LegacyNsfw/AvcsController/Docs/2013 STI Signals.png

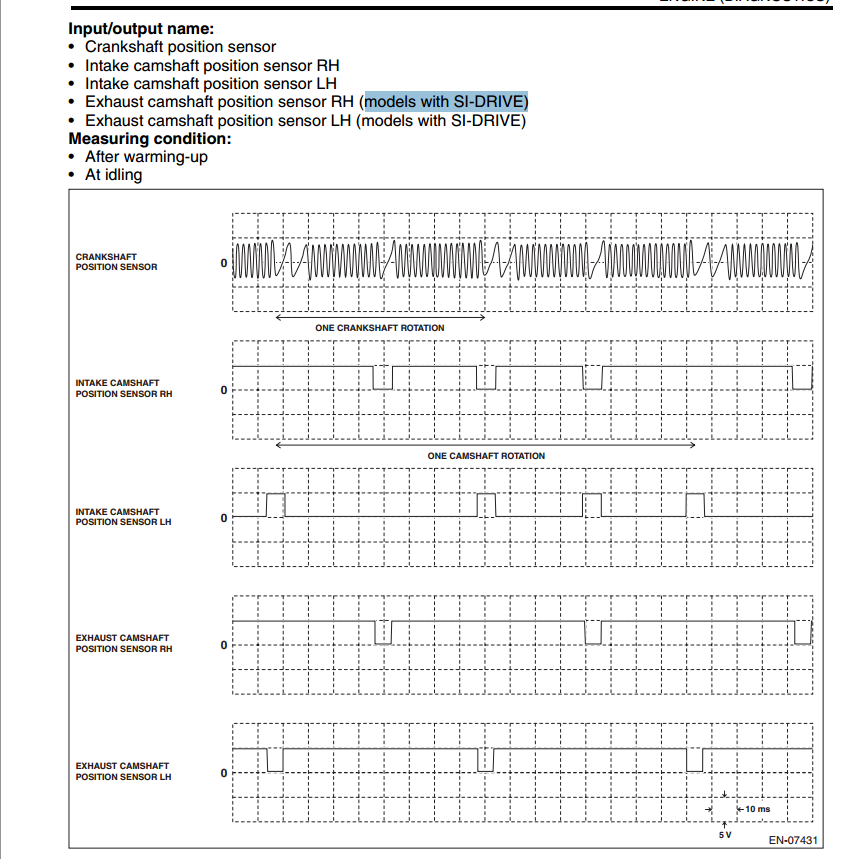
Docs/2013 STI Signals.png
