LegacyNsfw/AvcsController/Docs/US04AVCS.jpg

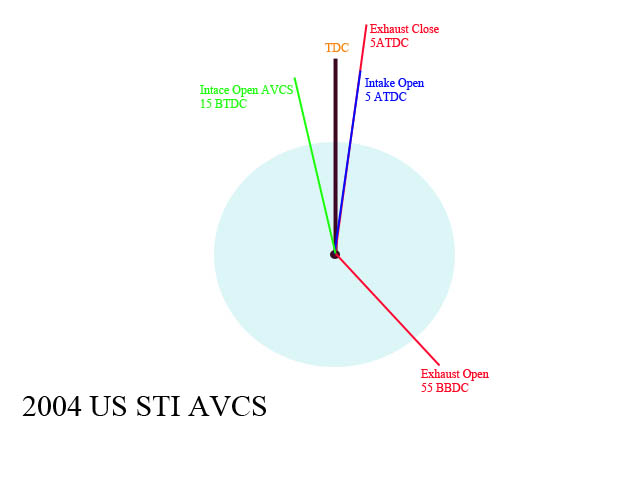
Docs/US04AVCS.jpg
