LegacyNsfw/AvcsController/Docs/US08AVCS.jpg

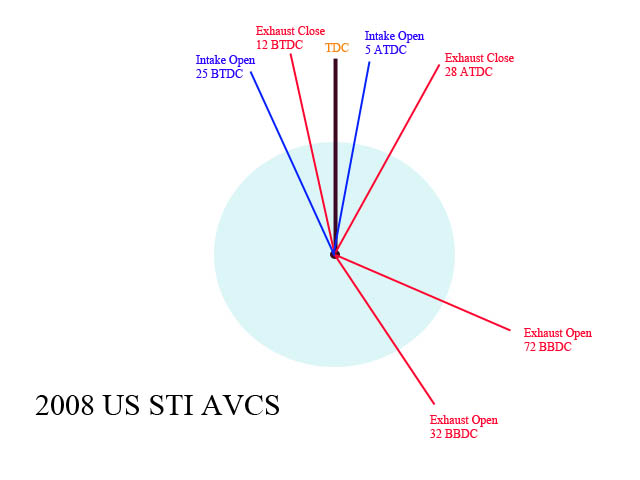
Docs/US08AVCS.jpg
