LegacyNsfw/AvcsController/Images/CrankSensor_CaseMounted.jpg

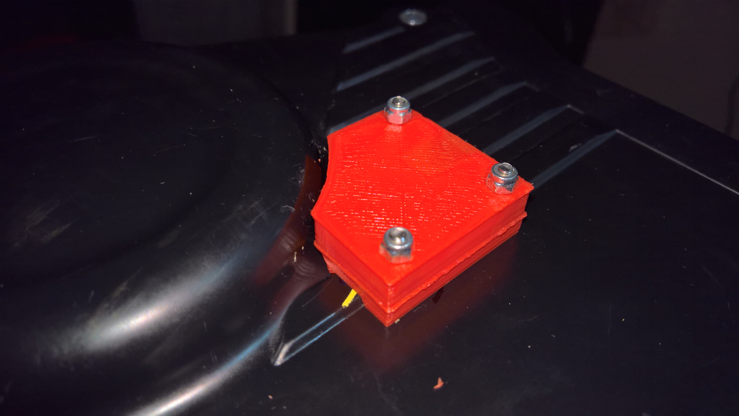
Images/CrankSensor_CaseMounted.jpg
