LegacyNsfw/AvcsController/Images/Scope_CamSensorNoiseAndFiltering.jpg

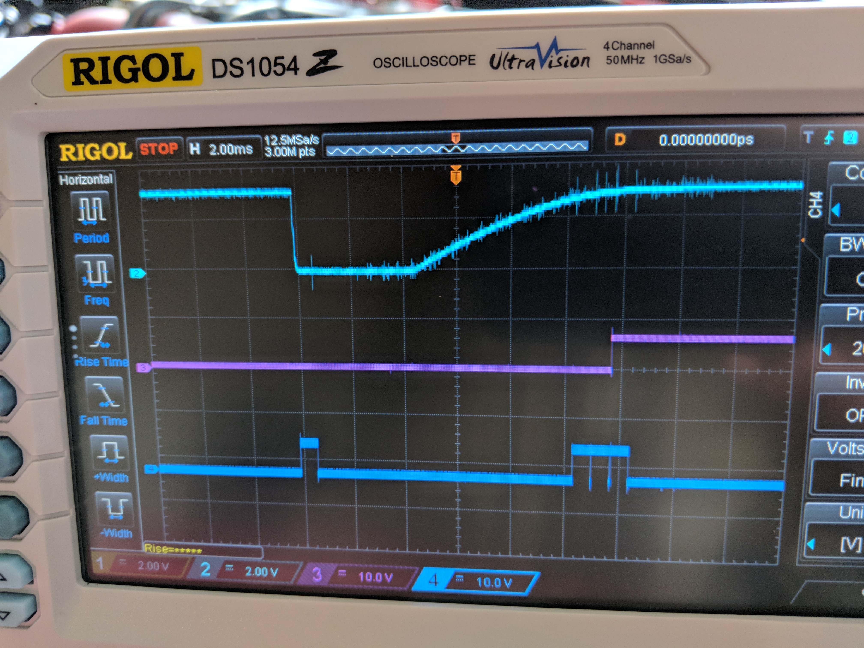
Images/Scope_CamSensorNoiseAndFiltering.jpg
