LegacyNsfw/AvcsController/Images/Scope_CrankSensorOscillation.jpg

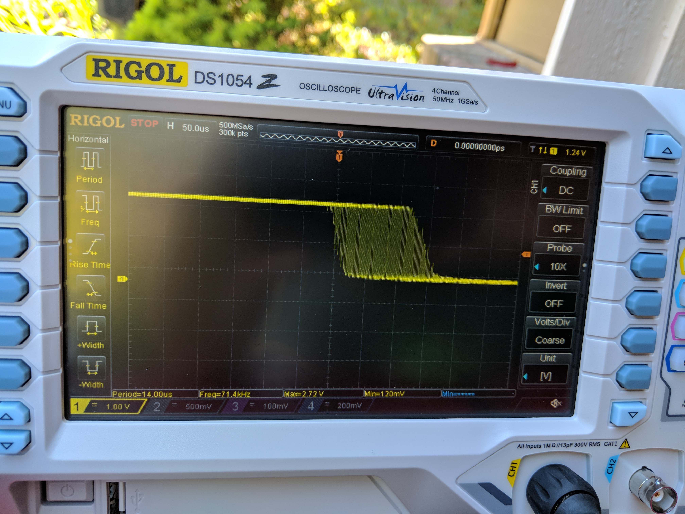
Images/Scope_CrankSensorOscillation.jpg
