LegacyNsfw/AvcsController/Code/Controller/DFR_Key.cpp

#include "Arduino.h"
#include "DFR_Key.h"

static int DEFAULT_KEY_PIN = 0;
static int DEFAULT_THRESHOLD = 50;

static int UPKEY_ARV = 221; //that's read "analogue read value"
static int DOWNKEY_ARV = 506;
static int LEFTKEY_ARV = 773;
static int RIGHTKEY_ARV = 0;
static int SELKEY_ARV = 880;
static int NOKEY_ARV = 1023;

DFR_Key::DFR_Key()
{
	_refreshRate = 10;
	_keyPin = DEFAULT_KEY_PIN;
	_threshold = DEFAULT_THRESHOLD;
	_keyIn = NO_KEY;
	_curInput = NO_KEY;
	_curKey = NO_KEY;
	_prevInput = NO_KEY;
	_prevKey = NO_KEY;
	_oldTime = 0;
	_iterations = 0;
}

int DFR_Key::getKeyRaw()
{
	if (millis() > _oldTime + _refreshRate)
	{
		_oldTime = millis();
		_prevInput = _curInput;
		_curInput = analogRead(_keyPin);

		if (_curInput == _prevInput)
		{
			_change = false;
			_curKey = _prevKey;
		}
		else
		{
			_change = true;
			_prevKey = _curKey;

			if (_curInput > UPKEY_ARV - _threshold && _curInput < UPKEY_ARV + _threshold) _curKey = UP_KEY;
			else if (_curInput > DOWNKEY_ARV - _threshold && _curInput < DOWNKEY_ARV + _threshold) _curKey = DOWN_KEY;
			else if (_curInput > RIGHTKEY_ARV - _threshold && _curInput < RIGHTKEY_ARV + _threshold) _curKey = RIGHT_KEY;
			else if (_curInput > LEFTKEY_ARV - _threshold && _curInput < LEFTKEY_ARV + _threshold) _curKey = LEFT_KEY;
			else if (_curInput > SELKEY_ARV - _threshold && _curInput < SELKEY_ARV + _threshold) _curKey = SELECT_KEY;
			else _curKey = NO_KEY;
		}

		if (_change) 
			return _curKey; 
		else 
			return SAMPLE_WAIT;

	//	_oldTime = millis();
	}
	else
	{
		return SAMPLE_WAIT;
	}
}

int ignore;

int DFR_Key::getKey()
{
	if (getKeyRaw() == SAMPLE_WAIT)
	{
		ignore = SAMPLE_WAIT;
		return SAMPLE_WAIT;
	}

	if (_curKey == NO_KEY)
	{
		ignore == NO_KEY;
		return NO_KEY;
	}

	if (_curKey == ignore)
	{
		return NO_KEY;
	}

	ignore = _curKey;
	return _curKey;
}

void DFR_Key::setRate(int rate)
{
	_refreshRate = rate;
}
