LegacyNsfw/AvcsController/Code/Controller/DFR_Key.h

#pragma once

#include "Arduino.h"

#define SAMPLE_WAIT -1
#define NO_KEY 0
#define UP_KEY 3
#define DOWN_KEY 4
#define LEFT_KEY 2
#define RIGHT_KEY 5
#define SELECT_KEY 1

class DFR_Key
{
public:
	DFR_Key();
	int getKey();
	void setRate(int);
private:
	int _refreshRate;
	int _keyPin;
	int _threshold;
	int _keyIn;
	int _curInput;
	int _curKey;
	int _prevInput;
	int _prevKey;
	boolean _change;
	unsigned long _oldTime;
	int _iterations;
	int getKeyRaw();
};
