LegacyNsfw/AvcsController/Code/Controller/MenuBuilder.h

#include "ScreenNavigator.h"

///////////////////////////////////////////////////////////////////////////////
// Combines multiple screens into a menu
///////////////////////////////////////////////////////////////////////////////
class MenuBuilder
{
public:
	static Screen* BuildMenu();
};
