LegacyNsfw/AvcsController/Code/Controller/PeriodicJobs.h

// Invokes jobs periodically

class IPeriodicJobs
{
public:
	static IPeriodicJobs* GetInstance();

	virtual void Initialize() = 0;
	virtual void Update() = 0;
};

///////////////////////////////////////////////////////////////////////////////
// Unit test suite entry point
///////////////////////////////////////////////////////////////////////////////
void SelfTestPeriodicJobs();
